HEAPLab/SELDestroyer/firmware/config.h

// PIC16F18325 Configuration Bit Settings

// 'C' source line config statements

#include "global.h"

// CONFIG1
#if USE_EXT_OSCILLATOR
    #pragma config FEXTOSC = HS    // FEXTOSC External Oscillator mode Selection bits (EC (external clock) for 100 kHz to 8 MHz)
    #pragma config RSTOSC = EXT4X   // Power-up default value for COSC bits (EXTOSC with 4x PLL, with EXTOSC operating per FEXTOSC bits)
#else
    #pragma config RSTOSC = HFINT32
#endif 
#pragma config CLKOUTEN = OFF   // Clock Out Enable bit (CLKOUT function is disabled; I/O or oscillator function on OSC2)
#pragma config CSWEN = OFF      // Clock Switch Enable bit (Writing to NOSC and NDIV is not allowed)
#pragma config FCMEN = OFF      // Fail-Safe Clock Monitor Enable (Fail-Safe Clock Monitor is disabled)

// CONFIG2
#pragma config MCLRE = ON       // Master Clear Enable bit (MCLR/VPP pin function is MCLR; Weak pull-up enabled)
#pragma config PWRTE = OFF      // Power-up Timer Enable bit (PWRT disabled)
#pragma config WDTE = ON        // Watchdog Timer Enable bits (WDT enabled; SWDTEN is ignored)
#pragma config LPBOREN = OFF    // Low-power BOR enable bit (ULPBOR disabled)
#pragma config BOREN = ON       // Brown-out Reset Enable bits (Brown-out Reset enabled, SBOREN bit ignored)
#pragma config BORV = LOW       // Brown-out Reset Voltage selection bit (Brown-out voltage (Vbor) set to 2.45V)
#pragma config PPS1WAY = ON     // PPSLOCK bit One-Way Set Enable bit (The PPSLOCK bit can be cleared and set only once; PPS registers remain locked after one clear/set cycle)
#pragma config STVREN = ON      // Stack Overflow/Underflow Reset Enable bit (Stack Overflow or Underflow will cause a Reset)
#pragma config DEBUG = OFF      // Debugger enable bit (Background debugger disabled)

// CONFIG3
#pragma config WRT = OFF        // User NVM self-write protection bits (Write protection off)
#pragma config LVP = ON         // Low Voltage Programming Enable bit (Low Voltage programming enabled. MCLR/VPP pin function is MCLR. MCLRE configuration bit is ignored.)

// CONFIG4
#pragma config CP = OFF         // User NVM Program Memory Code Protection bit (User NVM code protection disabled)
#pragma config CPD = OFF        // Data NVM Memory Code Protection bit (Data NVM code protection disabled)

// #pragma config statements should precede project file includes.
// Use project enums instead of #define for ON and OFF.

#include <xc.h>
