HEAPLab/SELDestroyer/firmware/ina233.c

#include "ina233.h"
#include "i2c.h"

#include "global.h"

#define INA233_RESTORE_DEFAULT 0x12
#define INA233_ADC_CONFIG 0xD0
#define INA233_MFR_CAL 0xD4
#define INA233_MFR_ID 0x99
#define INA233_READ_VIN 0x88    // Retrieves the measurement for the VBUS voltage
#define INA233_READ_IIN 0x89     // Retrieves the input current measurement

#define INA233_OC_LIMIT 0x4A
#define INA233_OC_CLEAR 0x03
#define INA233_MFR_ALERT_MASK 0xD2


// Computation for the INA233
// Max current: 10A
// Current_LSB = (2^4)/(2^15) = 2^(-11)
// MFR_CALIBRATION = 0.00512 / (2^(-11) * 0.002) = 5243 = 0x147B
#define INA233_CURRENT_LSB_M1 0x1p11F
#define INA233_MFR_CALIBRATION 0x147B

#define INA233_ADDRESS 0b1000101


void ina233_init(void) {
    const uint8_t command = INA233_RESTORE_DEFAULT;

    bool val = i2c_send(INA233_ADDRESS, &command, 1);
    
    if(!val) {
        throw_fatal_exception();
    }
    
    // Config the scale coefficient
    const uint8_t register_and_data[3] = { 
        INA233_MFR_CAL,
        (INA233_MFR_CALIBRATION & 0x00FF),
        ((INA233_MFR_CALIBRATION & 0xFF00) >> 8)
    };

    val = i2c_send(INA233_ADDRESS, register_and_data, 3);

    if(!val) {
        throw_fatal_exception();
    }

    
    // And config the ADC
    const uint8_t register_and_data_2[3] = { 
        INA233_ADC_CONFIG,
        0b00000111,
        0b00000000 // UUUU[AVG]
    };

    val = i2c_send(INA233_ADDRESS, register_and_data_2, 3);

    if(!val) {
        throw_fatal_exception();
    }

}

#define REG2VAL(x) ((int16_t)((((uint16_t)x[1]) << 8) | x[0]))

bool ina233_test(void) {

    uint8_t readed[3];
    uint8_t register_id = INA233_MFR_ID;
    uint8_t stat = i2c_send_recv(INA233_ADDRESS, &register_id, 1, readed, 3);

    if(stat==0) {
        if(readed[0] == 2 && readed[1] == 0x54 && readed[2] == 0x49) {
            return true;
        }
    }
    
    return false;
}

void ina233_oc_set_limit(uint16_t current_limit_mA) {
    
    uint8_t register_and_data[3];
    
    register_and_data[0] = INA233_OC_LIMIT;
    
    uint16_t value = ((uint16_t) ((uint32_t)current_limit_mA) * ((uint32_t)2048) / ((uint32_t)1000));

    register_and_data[1] = value & 0xFF;
    register_and_data[2] = (value & 0xFF00) >> 8;

    bool val = i2c_send(INA233_ADDRESS, register_and_data, 3);
    
    if(!val) {
        throw_fatal_exception();
    }

    register_and_data[0] = INA233_MFR_ALERT_MASK;
    register_and_data[1] = 0b11111011;
    val = i2c_send(INA233_ADDRESS, register_and_data, 2);
    
    if(!val) {
        throw_fatal_exception();
    }
    
}

void ina233_oc_disable(void) {
    uint8_t register_and_data[2];
    register_and_data[0] = INA233_MFR_ALERT_MASK;
    register_and_data[1] = 0b11111111;
    bool val = i2c_send(INA233_ADDRESS, register_and_data, 2);
    
    if(!val) {
        throw_fatal_exception();
    }

}

void ina233_oc_clear(void) {
    uint8_t byte = INA233_OC_CLEAR;
    bool val = i2c_send(INA233_ADDRESS, &byte, 1);
    
    if(!val) {
        throw_fatal_exception();
    }

}

ina233_res_t ina233_read(void) {
    ina233_res_t to_ret;
    uint8_t readed_vin[2];
    uint8_t readed_iin[2];
    uint8_t register_id;
    uint8_t status;
    
    
    to_ret.valid = true;
    
    register_id = INA233_READ_VIN;
    status = i2c_send_recv(INA233_ADDRESS, &register_id, 1, readed_vin, 2);

    if(status != 0) to_ret.valid = false;
        
    register_id = INA233_READ_IIN;
    status = i2c_send_recv(INA233_ADDRESS, &register_id, 1, readed_iin, 2);

    if(status != 0) to_ret.valid = false;
    
    to_ret.V = REG2VAL(readed_vin) * 10L / 8L;
    to_ret.I = -REG2VAL(readed_iin) * 1000L / 2048L;

    return to_ret;

}

void ina233_configure_mfr(uint16_t mfr_time_config) {
    uint8_t register_and_data[3] = { 
        INA233_ADC_CONFIG,
        mfr_time_config & 0x00FF,
        (mfr_time_config & 0xFF00) >> 8
    };

    i2c_send(INA233_ADDRESS, register_and_data, 3);
}
