HEAPLab/SELDestroyer/firmware/destroyer.h

#ifndef DESTROYER_H
#define	DESTROYER_H

#include <stdint.h>
#include <stdbool.h>

typedef struct destroyer_data_s {
    uint16_t I_limit; // in mA  // AAMMM
    int16_t count;
    bool dut_is_active; // Actual current value
    bool sel_to_manage;
    bool hold_timer_expired;
    uint16_t avg_mode;   // 0bAAABBBCCC - AAA: avg mode, BBB: voltage conv time, CCC: current conv time - See INA233 datasheet
    uint8_t out_status; // 0x00 - Always OFF, 0xEE - always ON, 0xAA - auto
    uint16_t T_hold_us; // in 100 us // SMMMU 6.5535
    uint16_t T_hold_tick;   // in 128us
    
} destroyer_data_t;


#define DESTROYER_OUT_STATUS_OFF  0x00
#define DESTROYER_OUT_STATUS_ON   0xEE
#define DESTROYER_OUT_STATUS_AUTO 0xAA

extern destroyer_data_t destroyer_data;

void destroyer_init(void);

void destroyer_clear_N_SELs(void);

void destroyer_sel_occurred(void);

void destroyer_update(void); 

void destroyer_save_I_lim(void);
void destroyer_save_T_lim(void);
void destroyer_save_AVG_mode(void);
void destroyer_save_OUT_stat(void);
void destroyer_apply_config(void);
void destroyer_check_sel_end(void);

#endif
